SpectralVectors/BlenderMacroBoard/KiCAD_Gerber_Files/BlenderMacroBoardPCB.sch

## KiCad design KiCAD_Gerber_Files/BlenderMacroBoardPCB.sch (2022-11-03)

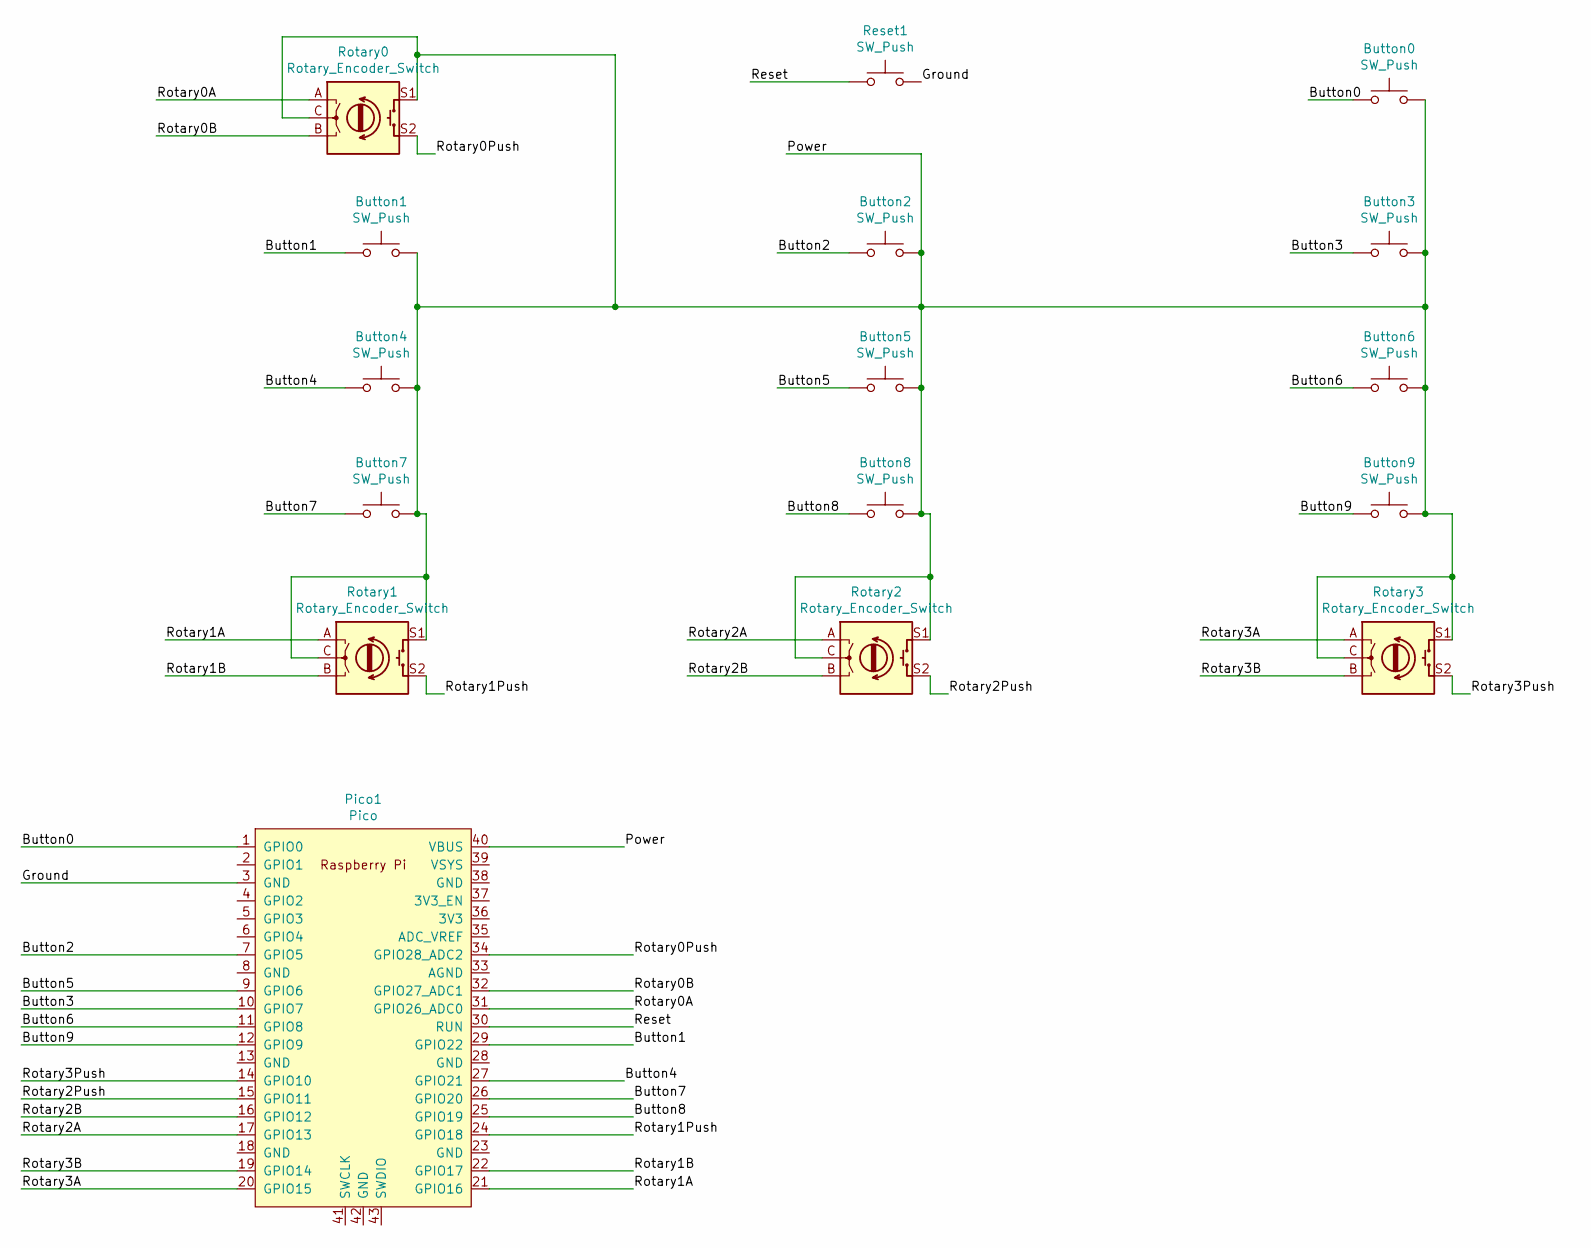
[picture p4: schematic BlenderMacroBoardPCB.sch]

Parts:
Button0, Button1, Button2, Button3, Button4, Button5, Button6, Button7, Button8, Button9: SW_Push; SW_Cherry_MX_1.00u_PCB
Pico1: Pico; RPi_Pico_SMD_TH
Reset1: SW_Push; SW_Cherry_MX_1.00u_PCB
Rotary0, Rotary1, Rotary2, Rotary3: Rotary_Encoder_Switch; RotaryEncoder_Alps_EC11E-Switch_Vertical_H20mm

Connections:
Button0: Button0.1, Pico1.1 (GPIO0)
Button1: Button1.1, Pico1.29 (GPIO22)
Button2: Button2.1, Pico1.7 (GPIO5)
Button3: Button3.1, Pico1.10 (GPIO7)
Button4: Button4.1, Pico1.27 (GPIO21)
Button5: Button5.1, Pico1.9 (GPIO6)
Button6: Button6.1, Pico1.11 (GPIO8)
Button7: Button7.1, Pico1.26 (GPIO20)
Button8: Button8.1, Pico1.25 (GPIO19)
Button9: Button9.1, Pico1.12 (GPIO9)
Ground: Pico1.3 (GND), Reset1.2
Power: Button0.2, Button1.2, Button2.2, Button3.2, Button4.2, Button5.2, Button6.2, Button7.2, Button8.2, Button9.2, Pico1.40 (VBUS), Rotary0.C, Rotary0.S1, Rotary1.C, Rotary1.S1, Rotary2.C, Rotary2.S1, Rotary3.C, Rotary3.S1
Reset: Pico1.30 (RUN), Reset1.1
Rotary0A: Pico1.31 (GPIO26_ADC0), Rotary0.A
Rotary0B: Pico1.32 (GPIO27_ADC1), Rotary0.B
Rotary0Push: Pico1.34 (GPIO28_ADC2), Rotary0.S2
Rotary1A: Pico1.21 (GPIO16), Rotary1.A
Rotary1B: Pico1.22 (GPIO17), Rotary1.B
Rotary1Push: Pico1.24 (GPIO18), Rotary1.S2
Rotary2A: Pico1.17 (GPIO13), Rotary2.A
Rotary2B: Pico1.16 (GPIO12), Rotary2.B
Rotary2Push: Pico1.15 (GPIO11), Rotary2.S2
Rotary3A: Pico1.20 (GPIO15), Rotary3.A
Rotary3B: Pico1.19 (GPIO14), Rotary3.B
Rotary3Push: Pico1.14 (GPIO10), Rotary3.S2
